laurent-colas/Light_control/CAD/On-Off switches/Documentation/Switches/GR5-626-6010.PDF

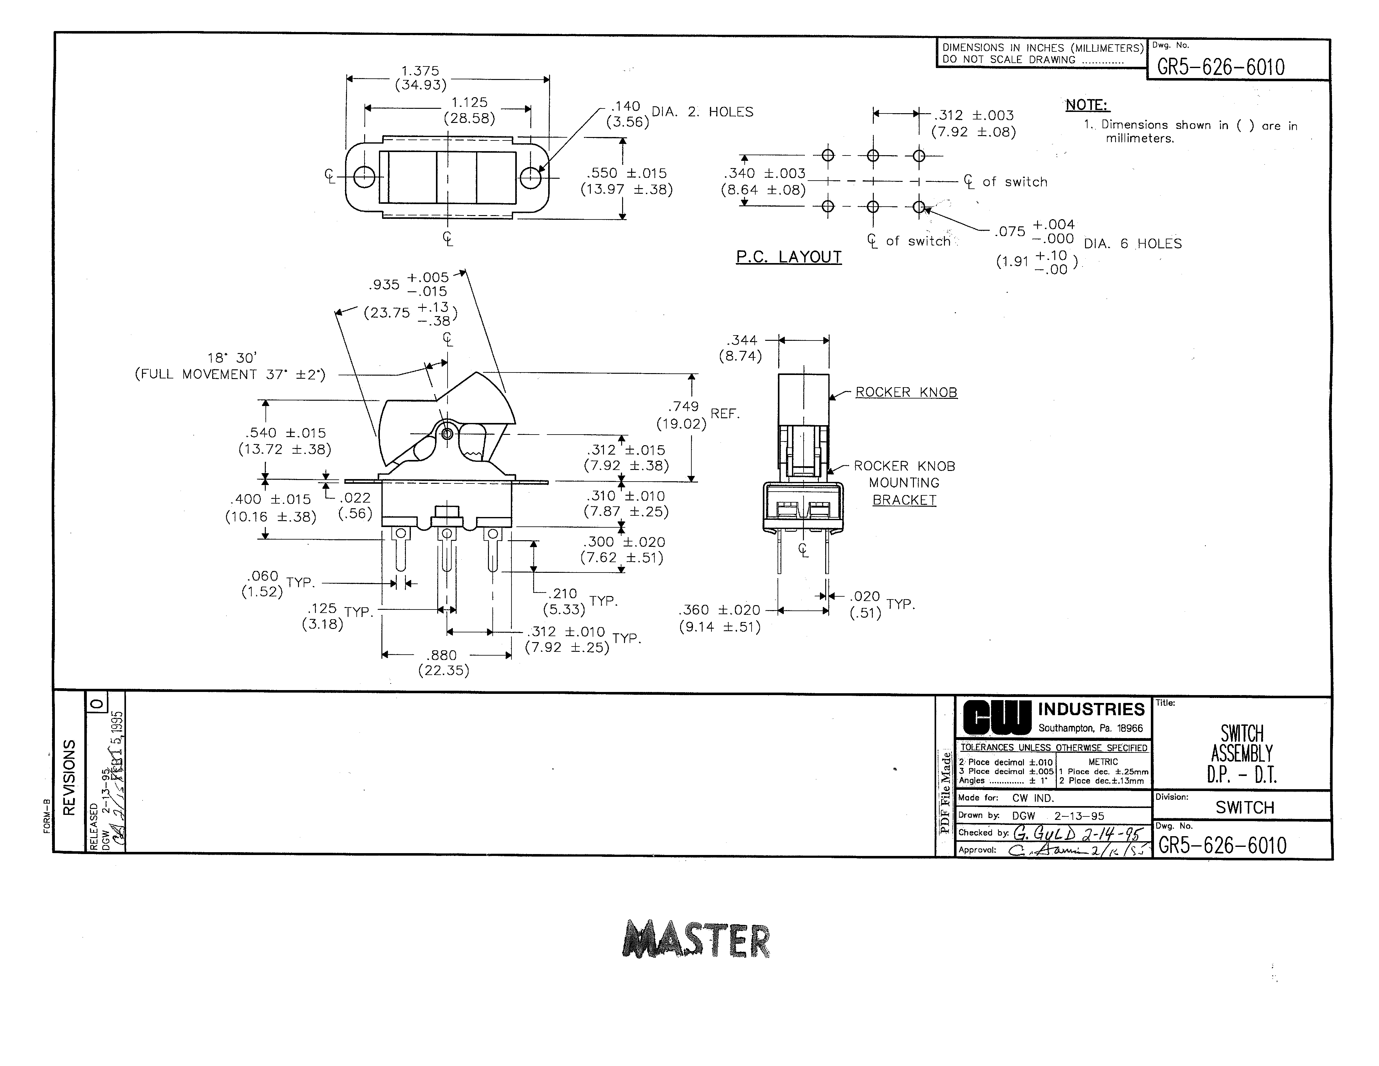
[picture p3: page 1]
