laurent-colas/Light_control/CAD/Motion Detector/Detector Case/Detector V2/boitier2.png

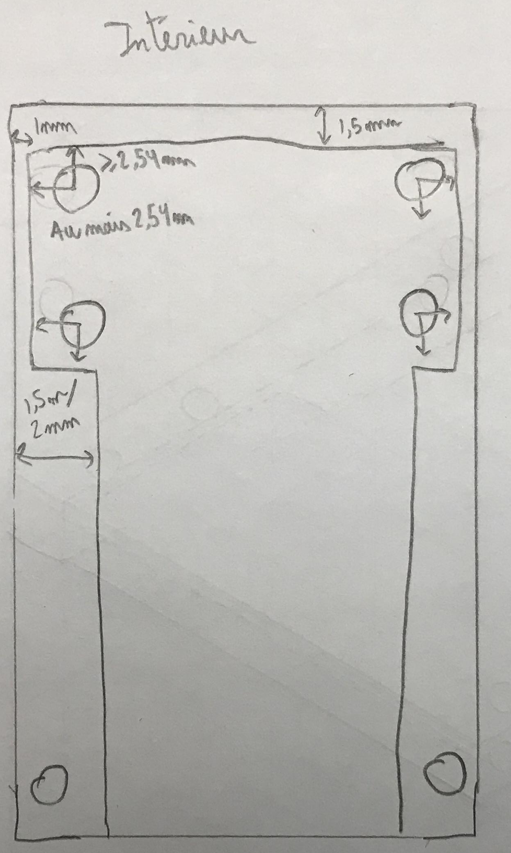
CAD/Motion Detector/Detector Case/Detector V2/boitier2.png
