laurent-colas/Light_control/CAD/Motion Detector/Detector Case/Detector V2/ISO_boitier2.jpg

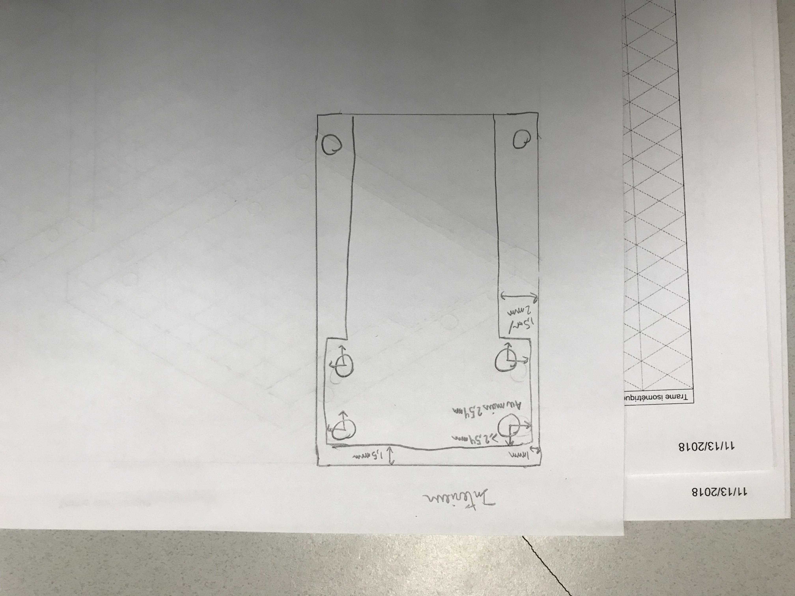
CAD/Motion Detector/Detector Case/Detector V2/ISO_boitier2.jpg
