laurent-colas/Light_control/CAD/Motion Detector/Doc PCB/Power Supply/apple_5W_brick_dim.JPG

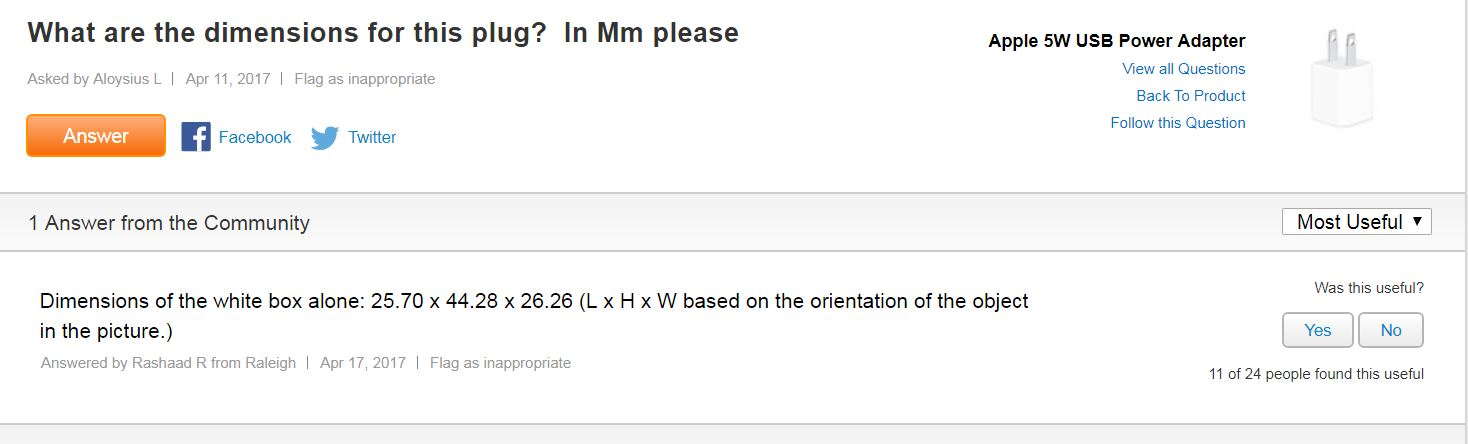
CAD/Motion Detector/Doc PCB/Power Supply/apple_5W_brick_dim.JPG
