laurent-colas/Light_control/CAD/Motion Detector/MotionDetectorV2/Images/ESP-01 motion detect circuit.JPG

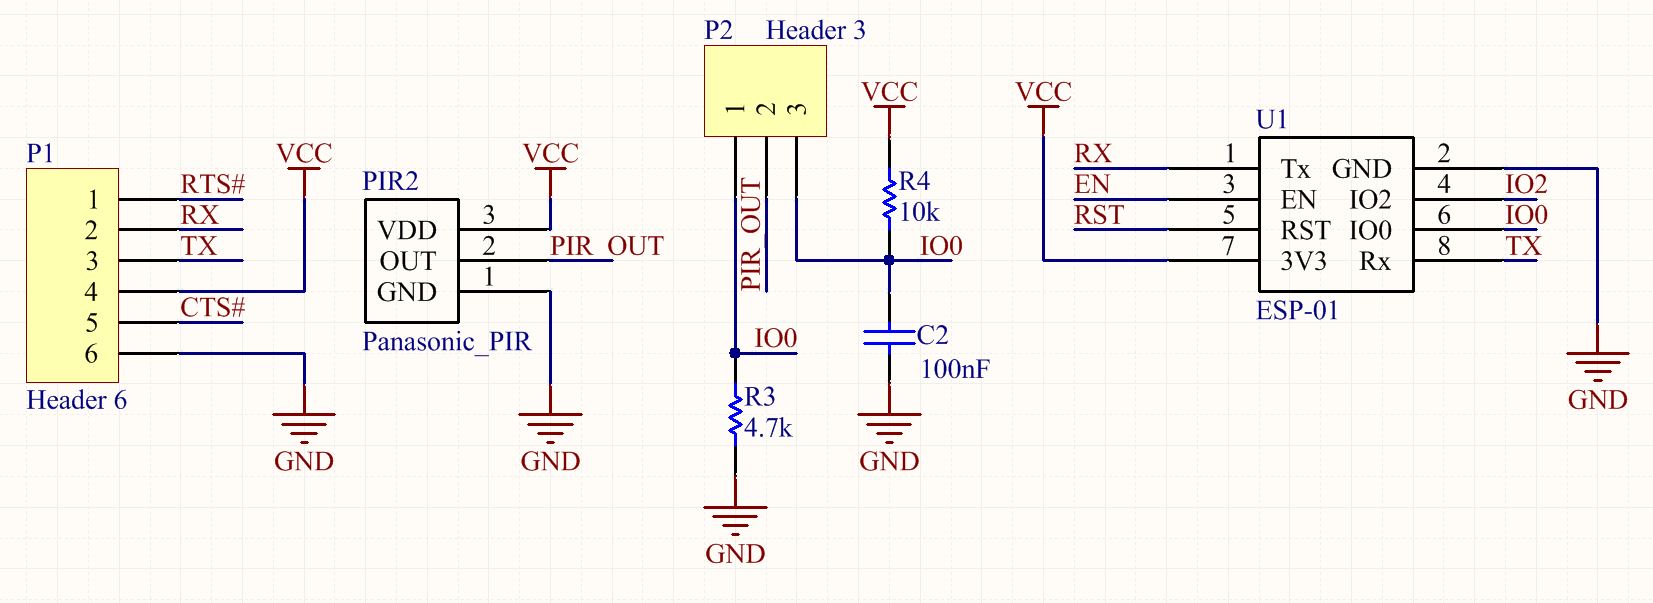
CAD/Motion Detector/MotionDetectorV2/Images/ESP-01 motion detect circuit.JPG
