laurent-colas/Light_control/CAD/Motion Detector/Doc PCB/bltn_eng_vz.pdf

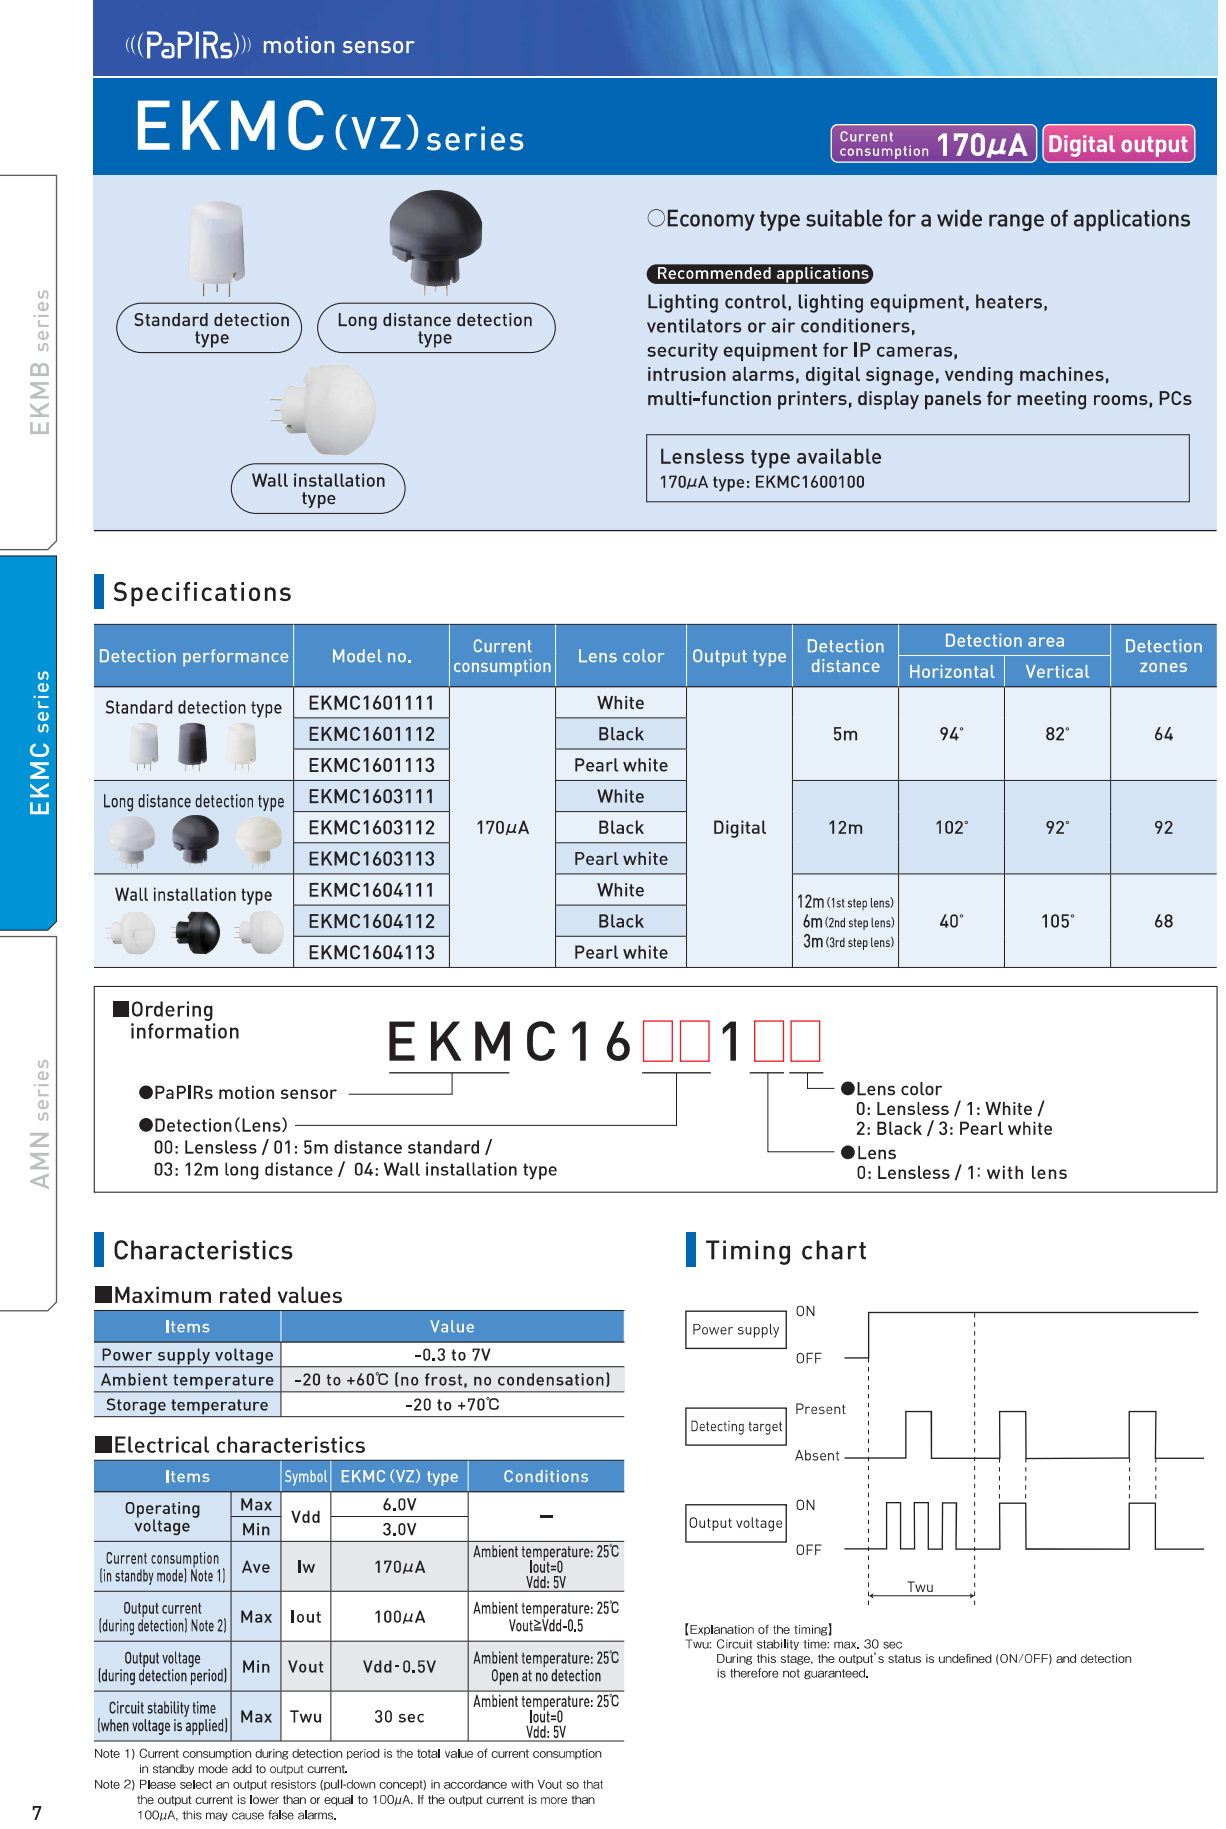
[picture p32: page 1]

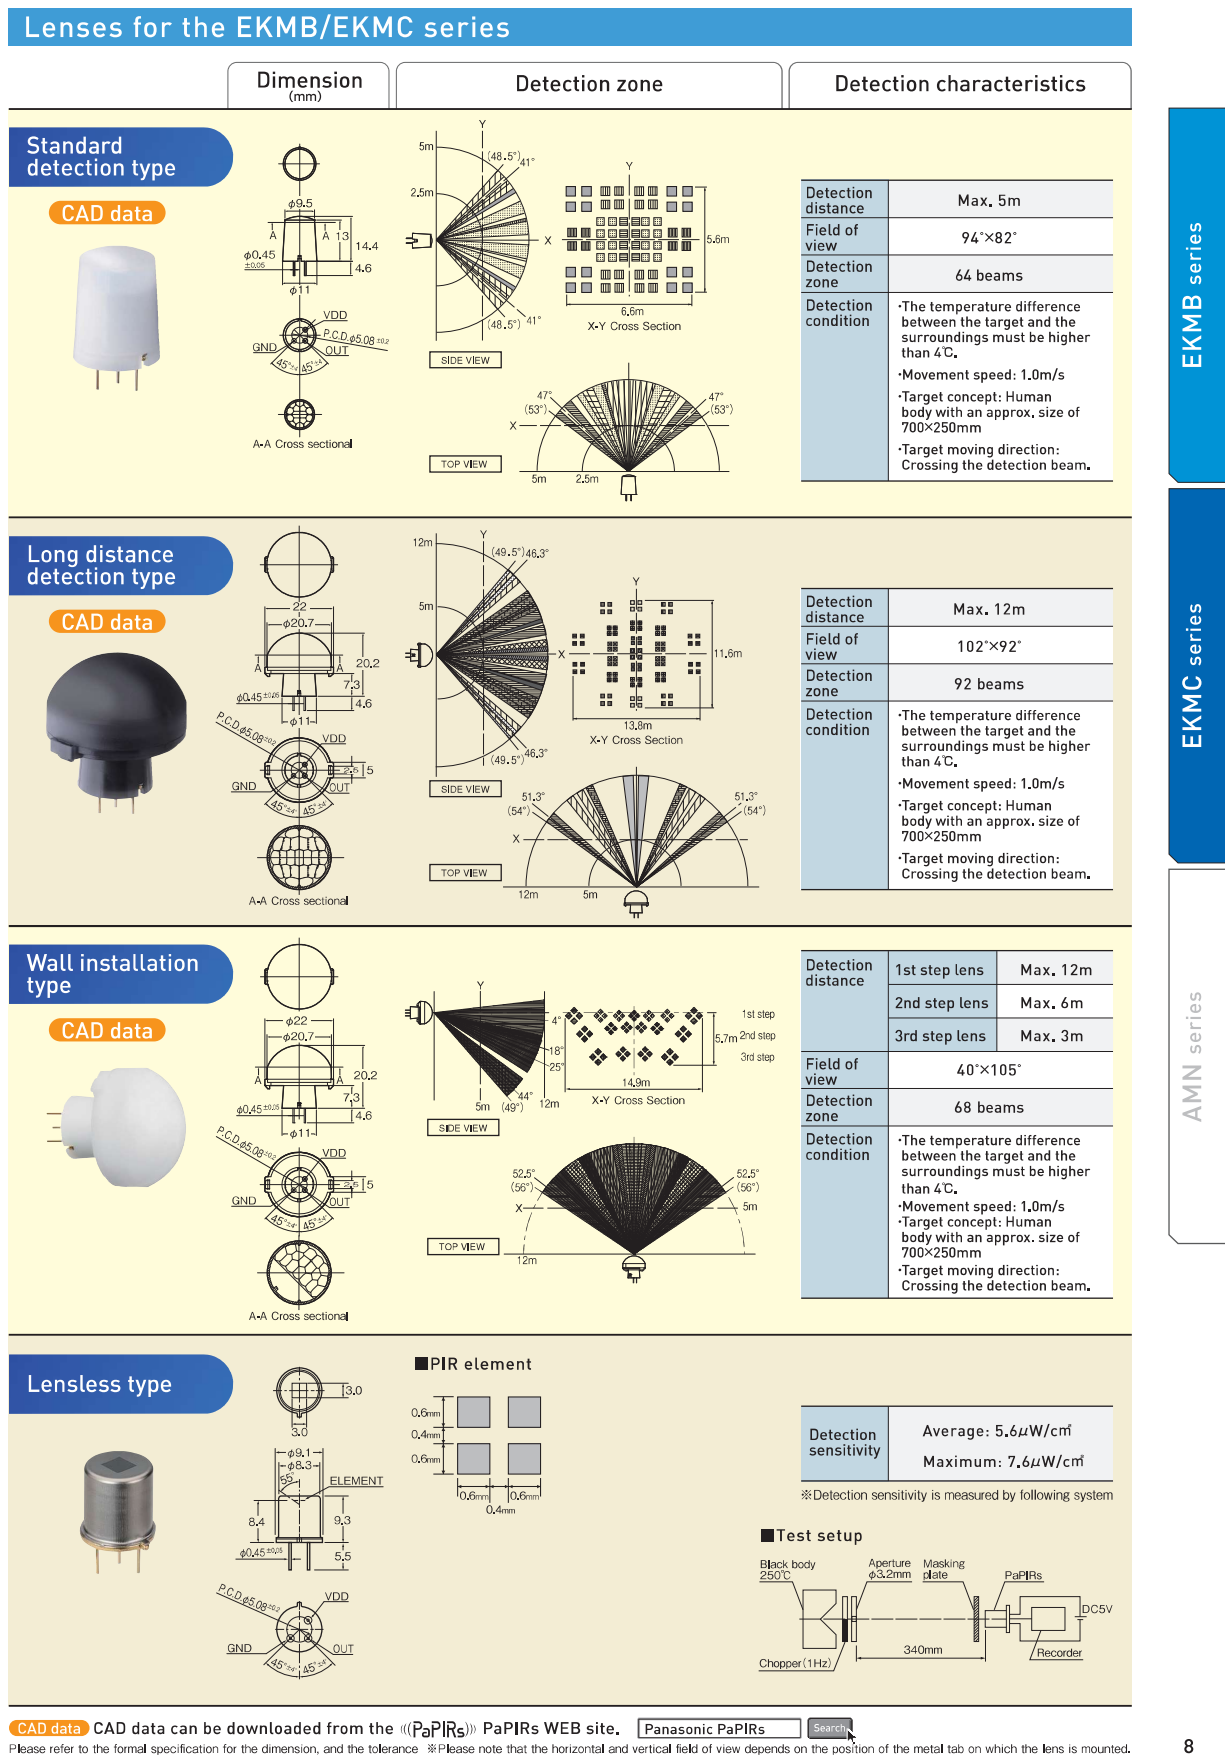
[picture p33: page 2]

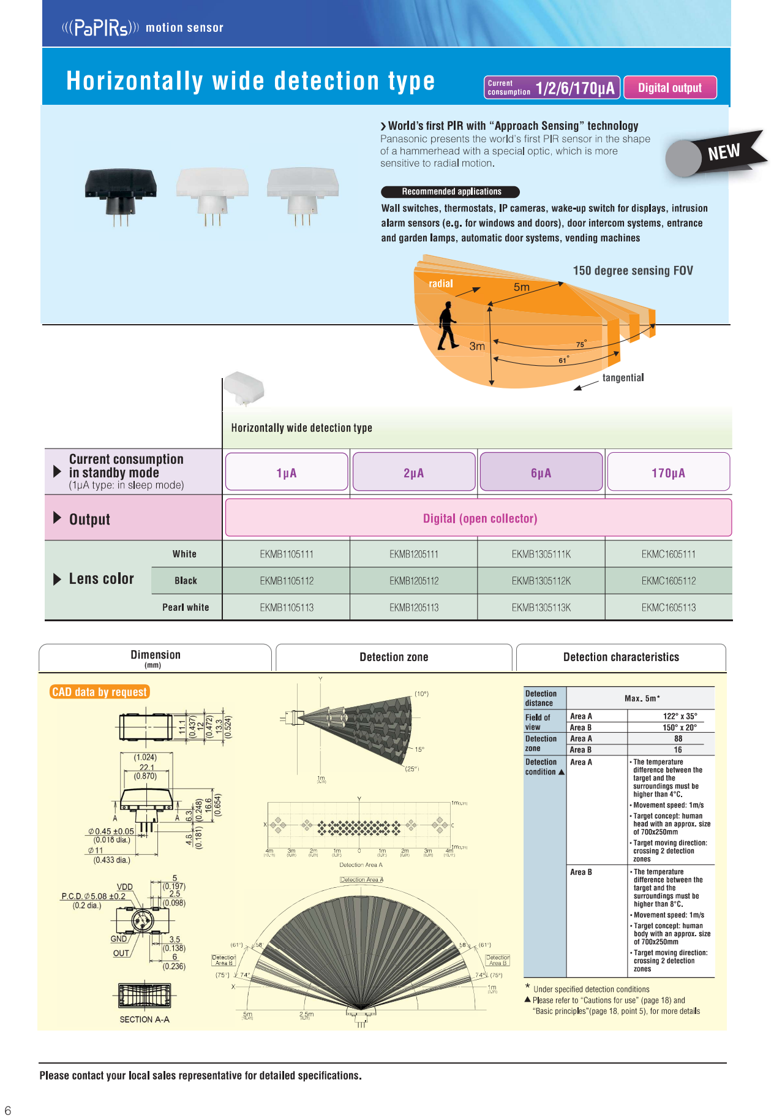
[picture p34: page 3]

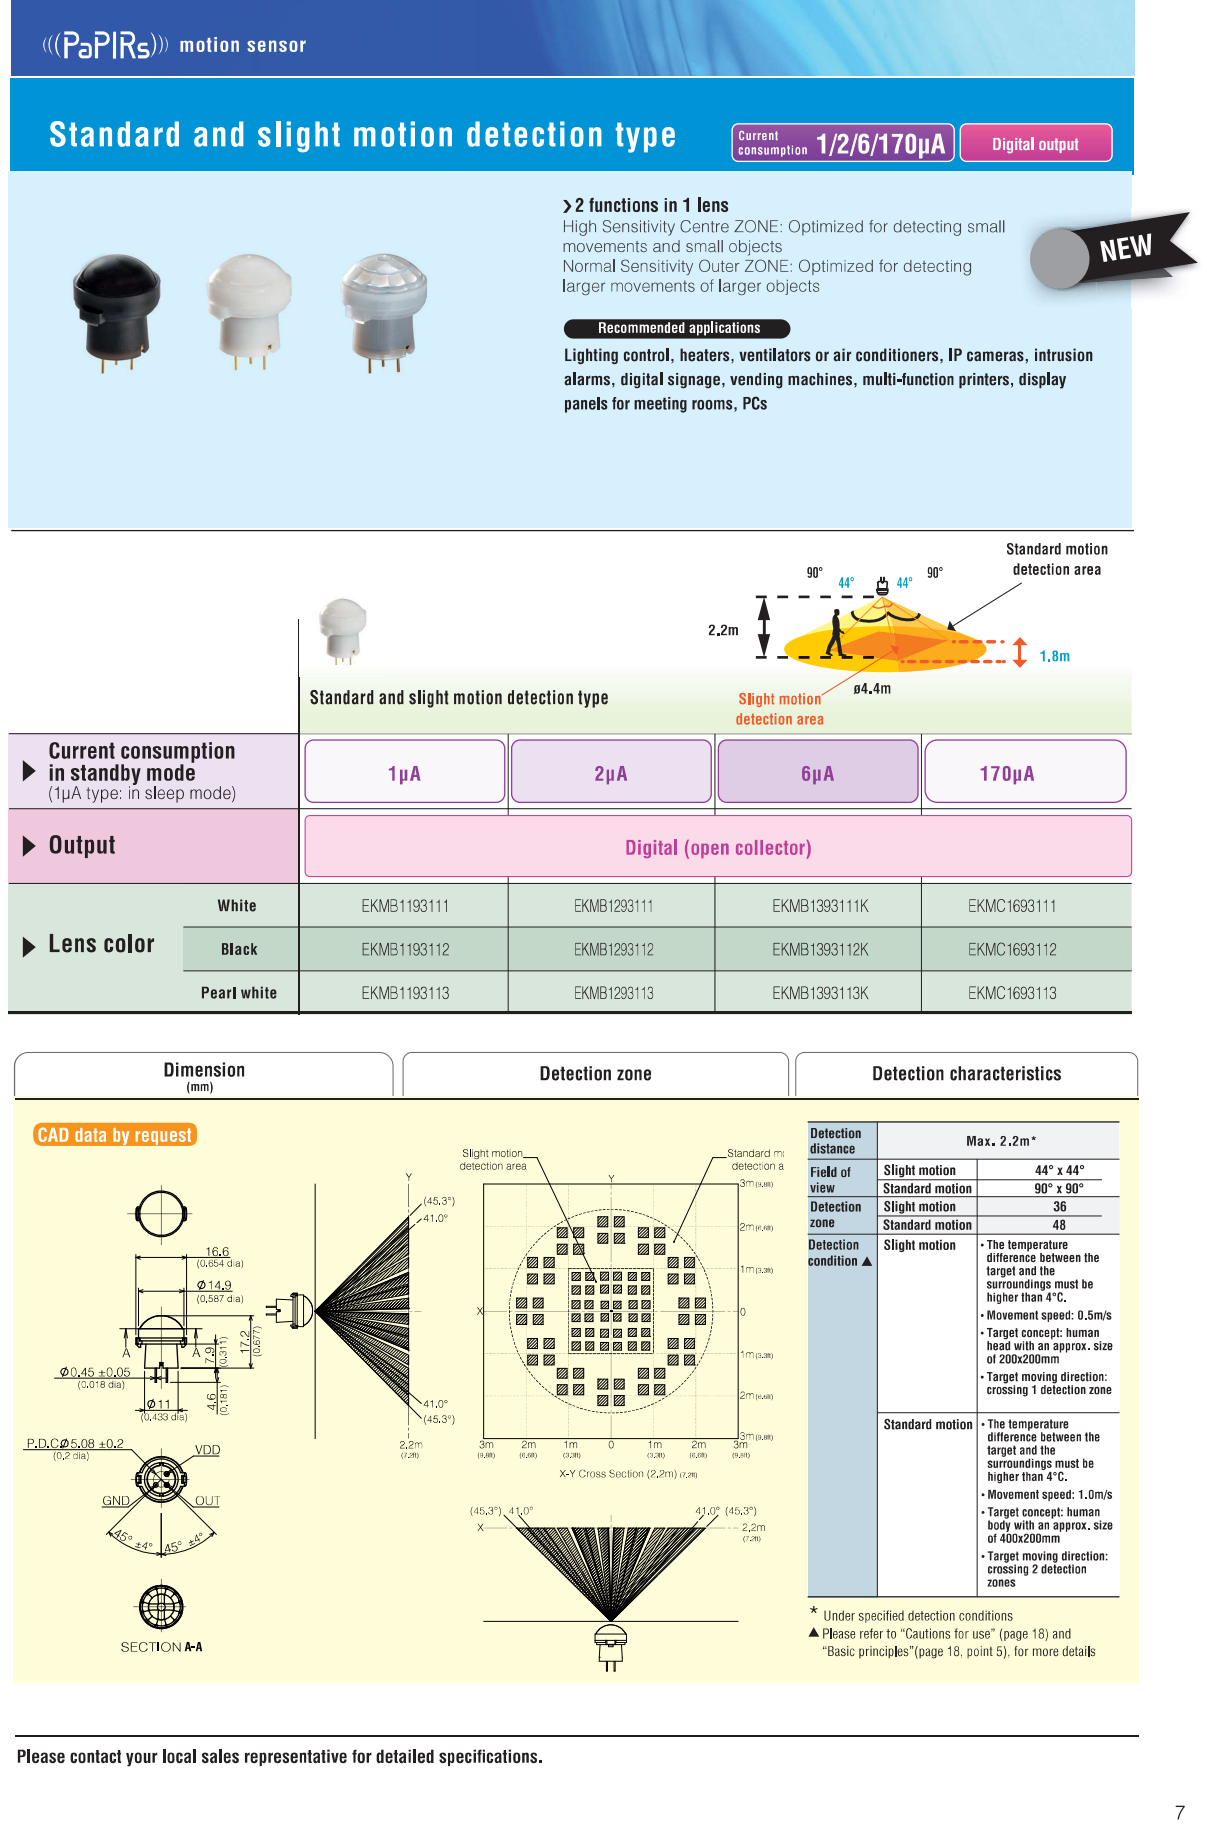
[picture p35: page 4]
